warthog9/ABQMMF-Solderkit-2017/greenchile - w-outline - indexed.bmp

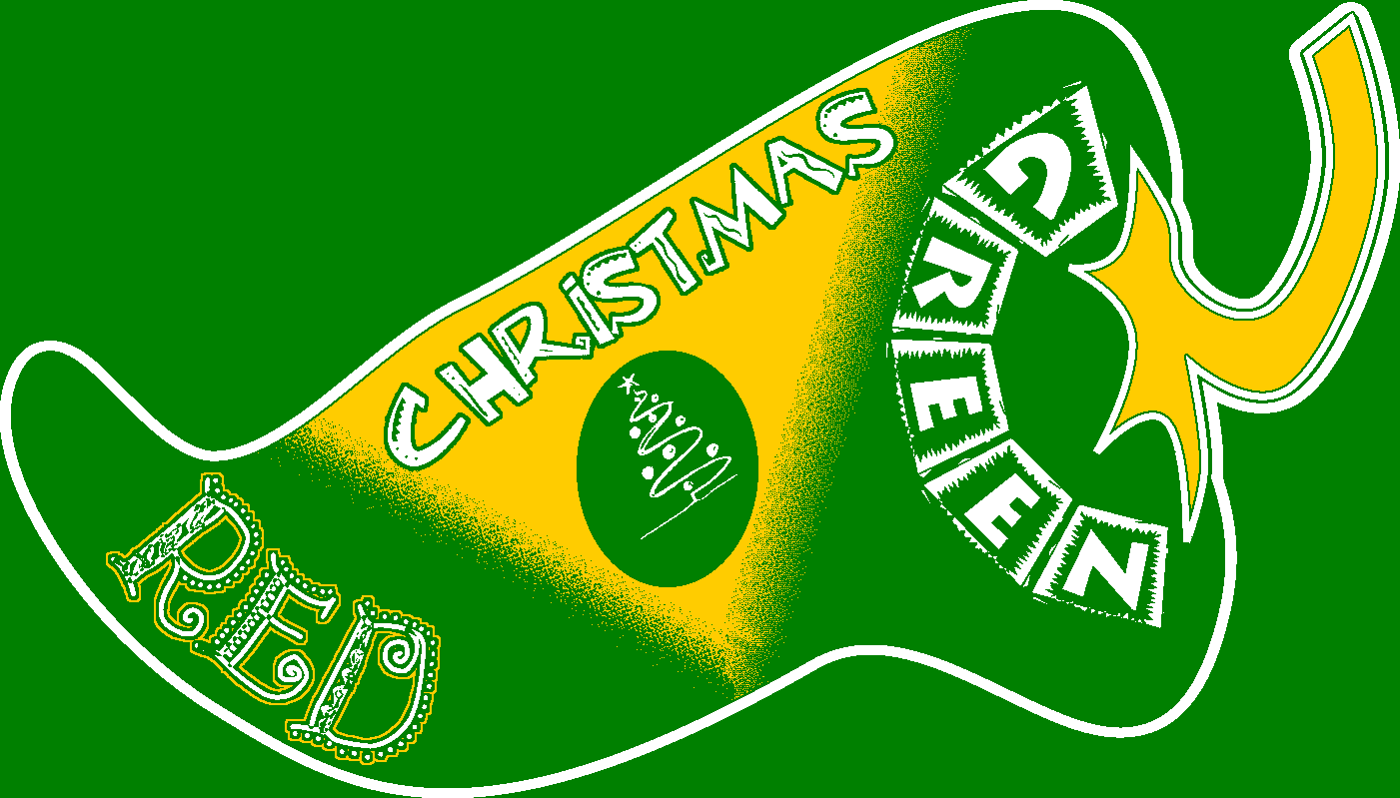
greenchile - w-outline - indexed.bmp
